davitkhlghatyan2010-afk/TaskNode/Hackpad.kicad_sch

## KiCad design Hackpad.kicad_sch (2026-06-03)

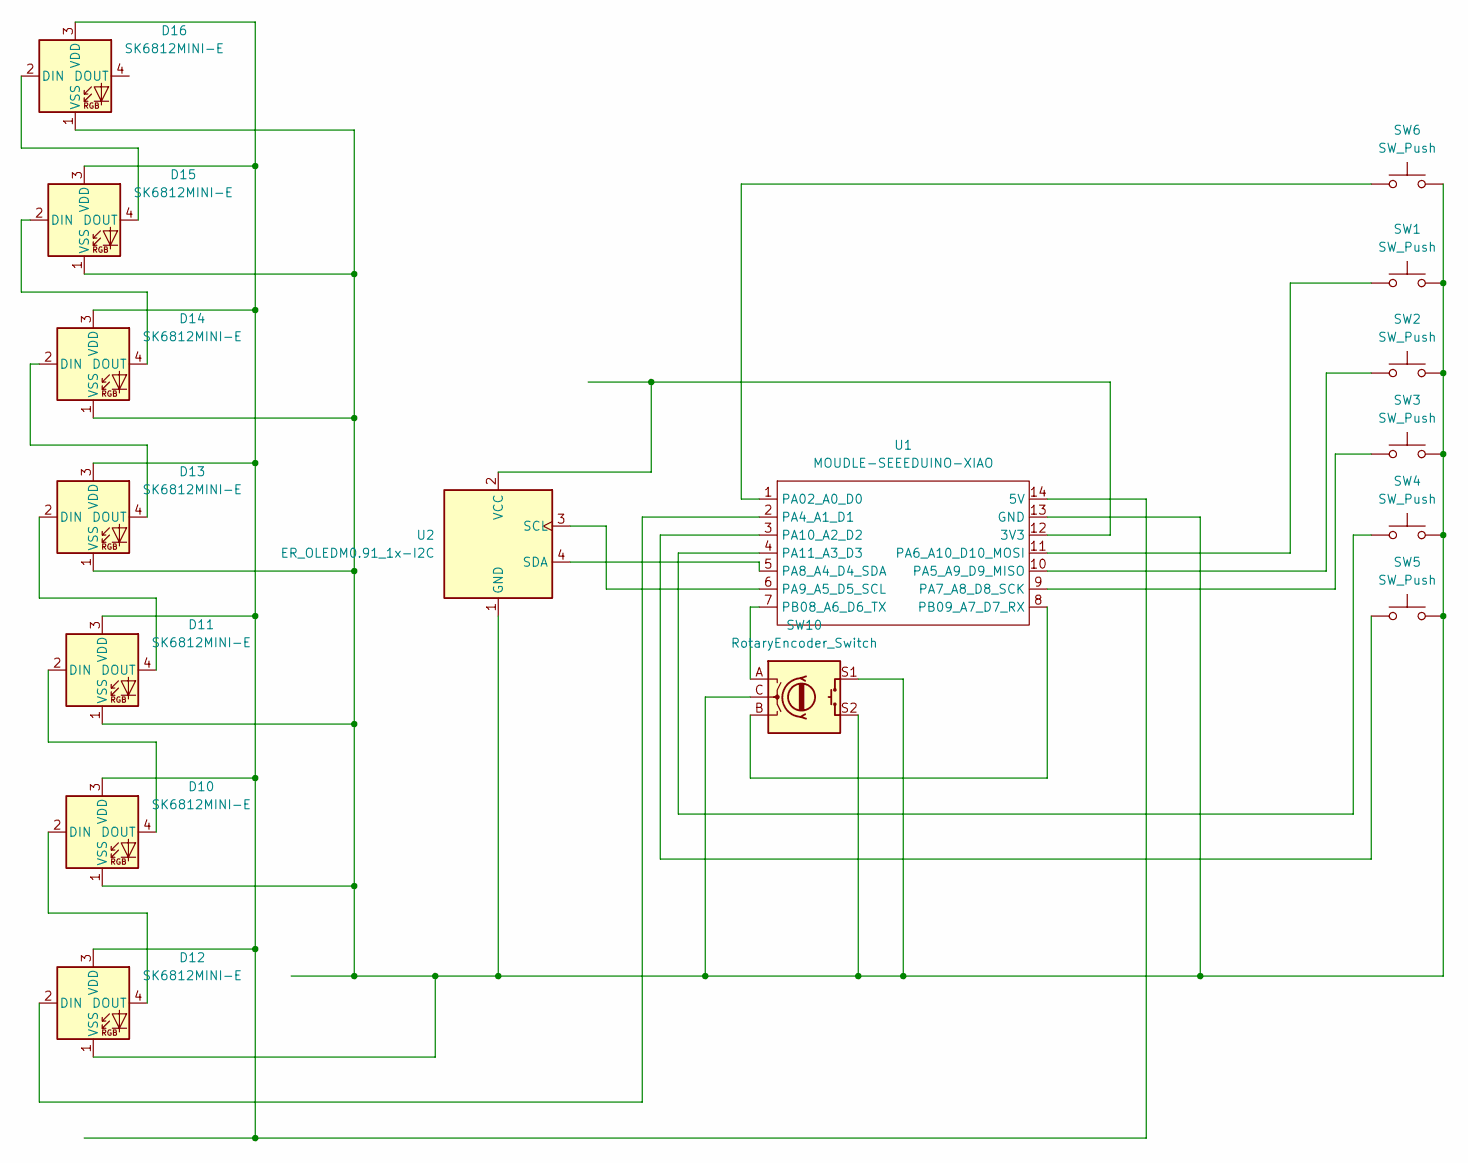
[picture p6: schematic Hackpad.kicad_sch]

Parts:
D10, D11, D12, D13, D14, D15, D16: SK6812MINI-E; LED_SK6812MINI-E_3.2x2.8mm_P1.5mm_ReverseMount
SW1, SW2, SW3, SW4, SW5, SW6: SW_Push; SW_Cherry_MX_1.00u_PCB
SW10: RotaryEncoder_Switch; RotaryEncoder_Alps_EC11E-Switch_Vertical_H20mm
U1: MOUDLE-SEEEDUINO-XIAO; XIAO-Generic-Hybrid-14P-2.54-21X17.8MM
U2: ER_OLEDM0.91_1x-I2C

Connections:
unnamed: D10.1 (VSS), D11.1 (VSS), D12.1 (VSS), D13.1 (VSS), D14.1 (VSS), D15.1 (VSS), D16.1 (VSS), SW1.2, SW2.2, SW3.2, SW4.2, SW5.2, SW6.2, SW10.C, SW10.S1, SW10.S2, U1.13 (GND), U2.1 (GND)
unnamed: D10.2 (DIN), D12.4 (DOUT)
unnamed: D10.3 (VDD), D11.3 (VDD), D12.3 (VDD), D13.3 (VDD), D14.3 (VDD), D15.3 (VDD), D16.3 (VDD), U1.14 (5V)
unnamed: D10.4 (DOUT), D11.2 (DIN)
unnamed: D11.4 (DOUT), D13.2 (DIN)
unnamed: D12.2 (DIN), U1.2 (PA4_A1_D1)
unnamed: D13.4 (DOUT), D14.2 (DIN)
unnamed: D14.4 (DOUT), D15.2 (DIN)
unnamed: D15.4 (DOUT), D16.2 (DIN)
unnamed: SW1.1, U1.11 (PA6_A10_D10_MOSI)
unnamed: SW2.1, U1.10 (PA5_A9_D9_MISO)
unnamed: SW3.1, U1.9 (PA7_A8_D8_SCK)
unnamed: SW4.1, U1.4 (PA11_A3_D3)
unnamed: SW5.1, U1.3 (PA10_A2_D2)
unnamed: SW6.1, U1.1 (PA02_A0_D0)
unnamed: SW10.A, U1.7 (PB08_A6_D6_TX)
unnamed: SW10.B, U1.8 (PB09_A7_D7_RX)
unnamed: U1.5 (PA8_A4_D4_SDA), U2.4 (SDA)
unnamed: U1.6 (PA9_A5_D5_SCL), U2.3 (SCL)
unnamed: U1.12 (3V3), U2.2 (VCC)
